deamonmist/WarcLock/Code/messages.h

/* WarcLock.ino — by Deamonmist (multi-file)
 * Random messages that will scroll across the screen from time to time.
 */

 #pragma once

 extern const char* g_messages[];
 extern const int g_messageCount;
